gumslone/zifra/zifra/src/configuration.h

#pragma once
#include <Arduino.h>
#include <ArduinoJson.h>
#include <FS.h>
#include "zifra_types.h"
#ifndef ZIFRA_CONFIGURATION_H
#define ZIFRA_CONFIGURATION_H

class ZifraConfig {
  public:
    static constexpr uint8_t ALARM_COUNT = 3;
    AlarmProperties alarms[ALARM_COUNT]{};
    Clock clock{};
    int alarmTimeoutMinutes{10}; // ringing auto-stops after this many minutes
    int utcOffsetInSeconds{2 * 3600};
    int dstMode{0}; // automatic summer time: 0 = off, 1 = EU, 2 = US
    String ntpServer{"pool.ntp.org"};
    String otaPassword{""}; // empty = firmware updates need no password
    bool wifiActive{true};
    bool DS3231_active{false};

    void setCb(std::function<void()> cb)
    {
      m_cb = cb;
    }
    void saveConfigCallback() {
      m_shouldSaveConfig = true;
    }
    void saveConfig(bool force = false) {
      // save the custom parameters to FS
      if (m_shouldSaveConfig || force) {
        DynamicJsonDocument json(4096);

        json["utcOffsetInSeconds"] = utcOffsetInSeconds;
        json["dstMode"] = dstMode;
        json["ntpServer"] = ntpServer;
        json["otaPassword"] = otaPassword;
        json["wifiActive"] = wifiActive;
        json["alarmTimeoutMinutes"] = alarmTimeoutMinutes;

        json["clock_12h"] = !clock.iso;
        json["clock_leading_hour_zero"] = clock.leadingHourZero;

        json["clock_sleep"] = clock.sleep;
        json["clock_sleep_start"] = clock.sleepStart;
        json["clock_sleep_finish"] = clock.sleepFinish;

        for (uint8_t i = 0; i < ALARM_COUNT; i++) {
          const String prefix = alarmPrefix(i);
          json[prefix + "Weekdays"] = join(alarms[i].weekdays, ",", 7);
          json[prefix + "Active"] = alarms[i].active;
          json[prefix + "Time"] = alarms[i].time;
          json[prefix + "Melody"] = alarms[i].melody;
        }

        File configFile = SPIFFS.open("/config.json", "w");
        serializeJson(json, configFile);
        configFile.close();
        D_println(F("Config saved"));
        // end save
      }
    }

    void loadConfig() {
      if (SPIFFS.exists("/config.json")) {
        // file exists, reading and loading
        File configFile = SPIFFS.open("/config.json", "r");

        if (configFile) {
          D_println(F("opened config file"));

          DynamicJsonDocument json(4096);
          const auto error = deserializeJson(json, configFile);

          if (!error) {
            JsonObject documentRoot = json.as<JsonObject>();
            setConfigParameters(documentRoot);

            D_println(F("Config loaded"));
          } else {
            switch (error.code()) {
              case DeserializationError::InvalidInput:
                D_println(F("Invalid input!"));
                break;
              case DeserializationError::NoMemory:
                D_println(F("Not enough memory"));
                break;
              default:
                D_println(F("Deserialization failed"));
                break;
            }
          }
        }
      } else {
        D_println(F("No configfile found, create a new file"));
        saveConfigCallback();
        saveConfig();
      }
    }

    // Applies and saves the new config. No restart: everything the clock
    // does reads the live config, and the time settings are re-applied
    // through the callback below.
    void setConfig(JsonObject &json) {
      setConfigParameters(json);
      saveConfigCallback();
      saveConfig();
    }

    String getConfig() {
      File configFile = SPIFFS.open("/config.json", "r");
      if (!configFile) {
        return "{}";
      }

      const size_t size = configFile.size();
      std::unique_ptr<char[]> buf(new char[size]);
      configFile.readBytes(buf.get(), size);

      DynamicJsonDocument root(4096);
      deserializeJson(root, buf.get());
      // never hand the update password to the UI - only whether one is set
      root.remove("otaPassword");
      root["otaPasswordSet"] = otaPassword.length() > 0;
      String json;
      serializeJson(root, json);
      return json;
    }

  private:

    bool m_shouldSaveConfig = false;
    std::function<void()> m_cb{nullptr};

    static String alarmPrefix(uint8_t index) {
      return "alarm" + String(index + 1);
    }
    void callback()
    {
      if (m_cb) {
        m_cb();
      }
    }
    void setConfigParameters(const JsonObject &json) {
      D_println("Config:");
      if (DEBUG) {
        for (JsonPair kv : json) {
          D_print(kv.key().c_str());
          D_print(" = ");
          D_println(kv.value().as<String>());
        }
        D_println();
      }
      setData(json, "wifiActive", wifiActive);
      setData(json, "utcOffsetInSeconds", utcOffsetInSeconds);
      setData(json, "dstMode", dstMode);
      if (dstMode < 0 || dstMode > 2) {
        dstMode = 0;
      }
      setData(json, "ntpServer", ntpServer);
      setData(json, "otaPassword", otaPassword);
      setData(json, "alarmTimeoutMinutes", alarmTimeoutMinutes);
      if (alarmTimeoutMinutes < 1) {
        alarmTimeoutMinutes = 1;
      }
      if (json.containsKey("clock_12h")) {
        clock.iso = !json["clock_12h"].as<bool>();
      }
      setData(json, "clock_leading_hour_zero", clock.leadingHourZero);
      setData(json, "clock_sleep", clock.sleep);
      setData(json, "clock_sleep_start", clock.sleepStart);
      setData(json, "clock_sleep_finish", clock.sleepFinish);

      for (uint8_t i = 0; i < ALARM_COUNT; i++) {
        const String prefix = alarmPrefix(i);
        if (json.containsKey(prefix + "Weekdays")) {
          createWeekdaysElements(json[prefix + "Weekdays"], alarms[i].weekdays);
        }
        setData(json, prefix + "Active", alarms[i].active);
        setData(json, prefix + "Time", alarms[i].time);
        setData(json, prefix + "Melody", alarms[i].melody);
      }

      // After the new values are in place, let the owner re-apply the ones
      // that need it (NTP offset/server) - the reason saving used to reboot.
      if (json.containsKey("utcOffsetInSeconds") || json.containsKey("ntpServer") ||
          json.containsKey("dstMode")) {
        callback();
      }
    }

    template<typename T>
    void setData(const JsonObject &json, const String& key, T & var)
    {
      if (json.containsKey(key)) {
        var = json[key].as<T>();
      }
    }

    // "0,1,1,1,1,1,0" -> arr[7]. Hand-rolled: sscanf would drag the whole
    // float-capable scanf family into the flash image.
    void createWeekdaysElements(const char *str, int *arr) {
      for (int i = 0; i < 7; i++) {
        arr[i] = (*str == '1') ? 1 : 0;
        while (*str && *str != ',') {
          str++;
        }
        if (*str == ',') {
          str++;
        }
      }
    }

}; // class Config

#endif
