gumslone/zifra/zifra/src/version.h

#pragma once
#ifndef ZIFRA_VERSION_H
#define ZIFRA_VERSION_H

// The firmware version, MAJOR.MINOR.PATCH. Single source of truth: the
// dashboard shows it, and the release workflow tags releases v<version>
// from it — bump it here for every release.
#define ZIFRA_VERSION "2.5.2"

#endif
